mrieker/hode/freecads/backpanandacc.FCStd

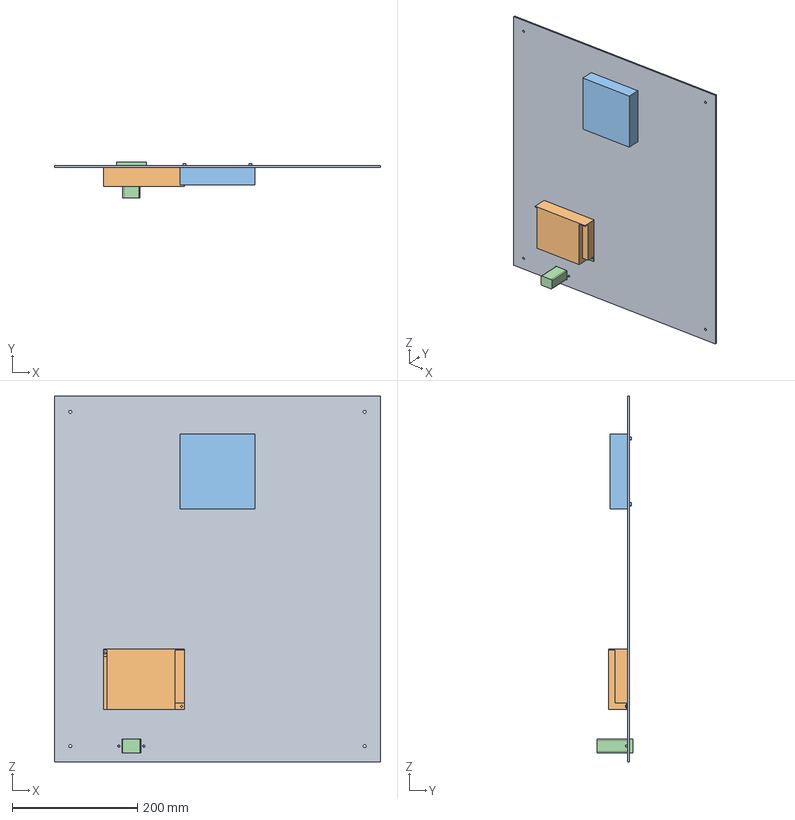
[picture p17: CAD file, 2022-03-06]
freecads/backpanandacc.FCStd
520.7 x 57.7 x 584.2 mm
backpanel_001
powersup_001
120mmfan_001
acpwrcon_001
