mrieker/hode/freecads/raspibrkt.FCStd

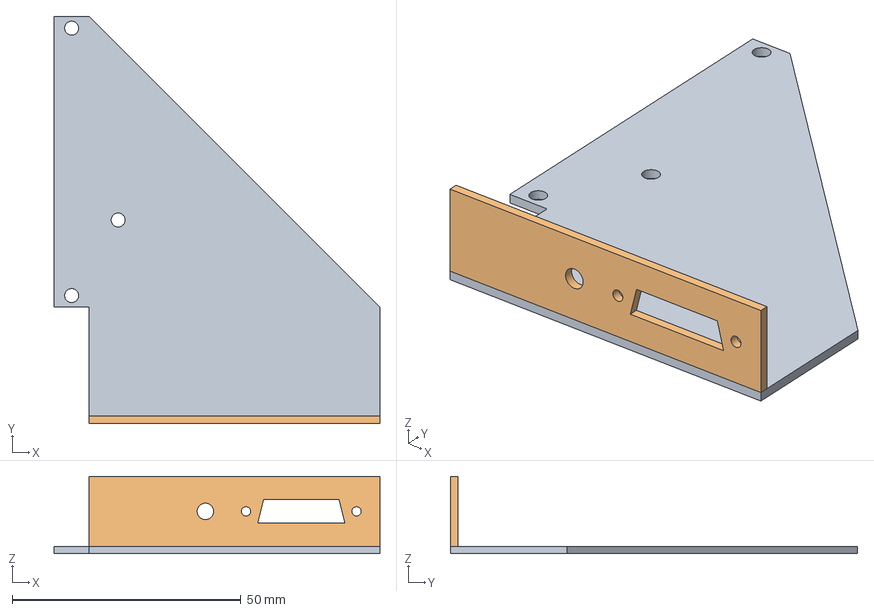
[picture p18: CAD file, 2022-03-06]
freecads/raspibrkt.FCStd
71.1 x 88.9 x 16.8 mm
raspi_base
raspi_cons
