mrieker/hode/freecads/backpanel.FCStd

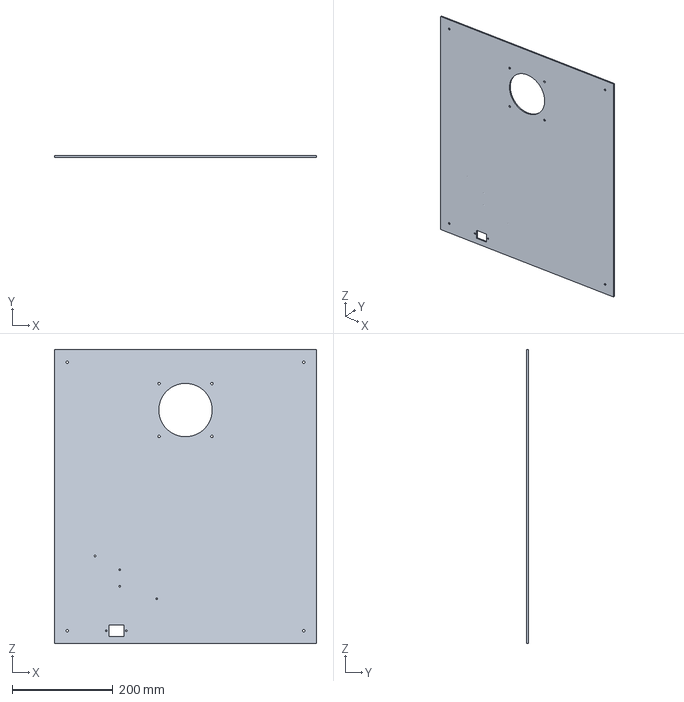
[picture p19: CAD file, 2022-03-06]
freecads/backpanel.FCStd
520.7 x 3.18 x 584.2 mm
