mrieker/hode/driver/raseqhaltloop.cc

//    Copyright (C) Mike Rieker, Beverly, MA USA
//    www.outerworldapps.com
//
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
//    EXPECT it to FAIL when someone's HeALTh or PROpeRTy is at RISk.
//
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
//    http://www.gnu.org/licenses/gpl-2.0.html

// do loop of halt instruction on RAS,SEQ board combination
// sequences through FETCH1,FETCH2,HALT1 states for electric testing
// optionally have LED board and C paddle
//  sudo insmod km/enabtsc.ko
//  . ./iow56sns.si
//  sudo -E ./raseqhaltloop.armv7l [-bpt] [-cpuhz 200]

// typically run at -cpuhz 500000
// does a SIGTRAP for gdb breakpoint at 100 errors

#include <signal.h>
#include <stdio.h>
#include <stdlib.h>
#include <string.h>
#include <time.h>

#include "gpiolib.h"
#include "miscdefs.h"

#define ST_RESET0  "RESET0",  0, G_READ | G_WRITE | G_HALT, 0, C_ALU_BONLY | C_MEM_WORD | C_PSW_IE
#define ST_RESET1  "RESET1",  0, G_READ | G_WRITE | G_HALT, C_BMUX_CON_0 | C_ALU_BONLY | C_GPRS_WE7 | C_PSW_WE | C__PSW_IECLR, C_MEM_WORD

#define ST_FETCH1  "FETCH1",  G_WORD | G_READ, G_WRITE | G_HALT, C_GPRS_REA7 | C_BMUX_CON_0 | C_ALU_ADD | C_MEM_READ | C_MEM_WORD, C_PSW_IE
#define ST_FETCH2  "FETCH2",  0, G_READ | G_WRITE | G_HALT, C_GPRS_REA7 | C_BMUX_CON_2 | C_ALU_ADD | C_GPRS_WE7 | C__IR_WE, C_MEM_WORD | C_PSW_IE

#define ST_BCC1    "BCC1",    0, G_READ | G_WRITE | G_HALT, C_GPRS_REA7 | C_BMUX_IRBROF | C_ALU_ADD, C_MEM_WORD | C_GPRS_WE7 | C_PSW_IE

#define ST_ARITH1  "ARITH1",  0, G_READ | G_WRITE | G_HALT, C_GPRS_REA | C_GPRS_REB | C_ALU_IRFC | C_GPRS_WED | C_PSW_ALUWE, C_MEM_WORD | C_PSW_IE

#define ST_STORE1  "STORE1",  G_WRITE, G_READ | G_HALT, C_GPRS_REA | C_BMUX_IRLSOF | C_ALU_ADD | C_MEM_WRITE, C_PSW_IE | C_MEM_WORD
#define ST_STORE2  "STORE2",  0, G_READ | G_WRITE | G_HALT, C_GPRS_RED2B | C_ALU_BONLY, C_MEM_WORD | C_PSW_IE

#define ST_LDA1    "LDA1",    0, G_READ | G_WRITE | G_HALT, C_GPRS_REA | C_BMUX_IRLSOF | C_ALU_ADD | C_GPRS_WED, C_MEM_WORD | C_PSW_IE

#define ST_LOAD1   "LOAD1",   G_READ, G_WRITE | G_HALT, C_GPRS_REA | C_BMUX_IRLSOF | C_ALU_ADD | C_MEM_READ, C_PSW_IE | C_MEM_WORD
#define ST_LOAD2   "LOAD2",   0, G_READ | G_WRITE | G_HALT, C_MEM_REB | C_ALU_BONLY | C_GPRS_WED, C_PSW_IE | C_MEM_WORD
#define ST_LOAD3   "LOAD3",   0, G_READ | G_WRITE | G_HALT, C_GPRS_REA7 | C_BMUX_CON_2 | C_ALU_ADD | C_GPRS_WE7, C_MEM_WORD | C_PSW_IE

#define ST_IREQ1   "IREQ1",   G_WORD | G_WRITE, G_READ | G_HALT, C_BMUX_CON__4 | C_BMUX_CON_2 | C_ALU_BONLY | C_MEM_WRITE | C_MEM_WORD, C_PSW_IE
#define ST_IREQ2   "IREQ2",   0, G_READ | G_WRITE | G_HALT, C__PSW_REB | C_ALU_BONLY, C_MEM_WORD | C_PSW_IE
#define ST_IREQ3   "IREQ3",   G_WORD | G_WRITE, G_READ | G_HALT, C_BMUX_CON__4 | C_ALU_BONLY | C_MEM_WRITE | C_MEM_WORD, C_PSW_IE
#define ST_IREQ4   "IREQ4",   0, G_READ | G_WRITE | G_HALT, C__PSW_IECLR | C_GPRS_REA7 | C_BMUX_CON_0 | C_ALU_ADD, C_MEM_WORD
#define ST_IREQ5   "IREQ5",   0, G_READ | G_WRITE | G_HALT, C_BMUX_CON_2 | C_ALU_BONLY | C_GPRS_WE7, C_MEM_WORD

#define ST_HALT1   "HALT1",   G_HALT, G_READ | G_WRITE, C_HALT | C_GPRS_REB | C_ALU_BONLY, C_MEM_WORD | C_PSW_IE

#define ST_IRET1   "IRET1",   G_WORD | G_READ, G_WRITE | G_HALT, C_BMUX_CON__4 | C_ALU_BONLY | C_MEM_READ | C_MEM_WORD, C_PSW_IE
#define ST_IRET2   "IRET2",   0, G_READ | G_WRITE | G_HALT, C_MEM_REB | C_MEM_WORD | C_ALU_BONLY | C_GPRS_WE7, C_PSW_IE
#define ST_IRET3   "IRET3",   G_WORD | G_READ, G_WRITE | G_HALT, C_BMUX_CON__4 | C_BMUX_CON_2 | C_ALU_BONLY | C_MEM_READ | C_MEM_WORD, C_PSW_IE
#define ST_IRET4   "IRET4",   0, G_READ | G_WRITE | G_HALT, C_MEM_REB | C_MEM_WORD | C_ALU_BONLY | C_PSW_WE, C_PSW_IE

#define ST_WRPS1   "WRPS1",   0, G_READ | G_WRITE | G_HALT, C_GPRS_REB | C_ALU_BONLY | C_PSW_WE, C_MEM_WORD | C_PSW_IE

#define ST_RDPS1   "RDPS1",   0, G_READ | G_WRITE | G_HALT, C__PSW_REB | C_ALU_BONLY | C_GPRS_WED, C_MEM_WORD | C_PSW_IE

static GpioLib *gpio;
static uint64_t ncycles;

static void verifystate (char const *name, uint32_t gset, uint32_t gclr, uint32_t cset, uint32_t cign);

int main (int argc, char **argv)
{
    bool bptonerror = false;
    uint32_t cpuhz = DEFCPUHZ;

    setlinebuf (stdout);

    for (int i = 0; ++ i < argc;) {
        if (strcasecmp (argv[i], "-bpt") == 0) {
            bptonerror = true;
            continue;
        }
        if (strcasecmp (argv[i], "-cpuhz") == 0) {
            if ((++ i >= argc) || (argv[i][0] == '-')) {
                fprintf (stderr, "-cpuhz missing freq\n");
                return 1;
            }
            cpuhz = atoi (argv[i]);
            continue;
        }
        if (argv[i][0] == '-') {
            fprintf (stderr, "unknown option %s\n", argv[i]);
            return 1;
        }
        fprintf (stderr, "unknown argument %s\n", argv[i]);
        return 1;
    }

    gpio = new PhysLib (cpuhz);
    gpio->open ();

    gpio->writegpio (false, G_RESET);
    gpio->halfcycle ();
    gpio->halfcycle ();
    gpio->halfcycle ();
    gpio->writegpio (false, 0);
    verifystate (ST_RESET0);
    gpio->writegpio (false, 0);
    gpio->halfcycle ();
    ncycles ++;
    gpio->writegpio (false, G_CLK);
    gpio->halfcycle ();
    verifystate (ST_RESET1);

    uint32_t lasttime = time (NULL);
    uint64_t lastcycs = 0;

    uint32_t errors   = 0;
    uint32_t lastsamp = 0;

    uint16_t opcode   = 0x0070; // HALT %R7
    uint16_t nextpc   = 0;

    while (true) {
        uint32_t thistime = time (NULL);
        if (thistime / 60 > lasttime / 60) {
            printf ("%02u:%02u:%02u %4u %13llu cycles  %6llu Hz  %10.3f uS\n",
                        thistime / 3600 % 24, thistime / 60 % 60, thistime % 60,
                        errors, ncycles, (ncycles - lastcycs) / (thistime - lasttime),
                        (thistime - lasttime) * 1000000.0 / (ncycles - lastcycs));
            lasttime = thistime;
            lastcycs = ncycles;
        }

        // halfway through the cycle with clock still high, so drop clock
        // if previous cycle was FETCH1, we are probably halfway through FETCH2, so start sending opcode to be latched in IR

        if ((lastsamp & G_INS) == (G_WORD|G_READ)) {
            gpio->writegpio (true, opcode * G_DATA0);
        } else {
            gpio->writegpio (false, 0);
        }

        // wait for end of cycle then sample GPIO pins
        gpio->halfcycle ();
        uint32_t sample = gpio->readgpio ();

        // decode the input pins to see what cycle we are at
        switch (sample & G_INS) {

            // currently at end of FETCH1
            case G_WORD|G_READ: {
                if ((lastsamp & G_INS) != (G_WORD|G_HALT)) {
                    printf ("%4u %13llu FETCH1 not preceded by HALT: %08X %s\n", ++ errors, ncycles, lastsamp, GpioLib::decocon (CON_G, lastsamp).c_str ());
                }
                uint16_t pc = sample / G_DATA0;
                if (pc != nextpc) {
                    printf ("%4u %13llu FETCH1 PC is %04X expected %04X\n", ++ errors, ncycles, pc, nextpc);
                }
                nextpc = pc + 2;
                break;
            }

            // currently at end of FETCH2
            case G_WORD: {
                if ((lastsamp & G_INS) != (G_WORD|G_READ)) {
                    printf ("%4u %13llu FETCH2 not preceded by FETCH1: %08X %s\n", ++ errors, ncycles, lastsamp, GpioLib::decocon (CON_G, lastsamp).c_str ());
                }
                break;
            }

            // currently at end of HALT
            case G_WORD|G_HALT: {
                if ((lastsamp & G_INS) != (G_WORD)) {
                    printf ("%4u %13llu HALT not preceded by FETCH2: %08X %s\n", ++ errors, ncycles, lastsamp, GpioLib::decocon (CON_G, lastsamp).c_str ());
                }
                uint16_t pc = sample / G_DATA0;
                if (pc != nextpc) {
                    printf ("%4u %13llu HALT PC is %04X expected %04X\n", ++ errors, ncycles, pc, nextpc);
                }
                break;
            }

            default: {
                printf ("%4u %13llu unknown cycle: %08X %s\n", ++ errors, ncycles, lastsamp, GpioLib::decocon (CON_G, lastsamp).c_str ());
                break;
            }
        }
        if (errors > 99) {
            if (! bptonerror) break;
            raise (SIGTRAP);
        }
        lastsamp = sample;

        // at end of cycle with clock still low, drive clock high
        // if we are ending FETCH2, keep outputting the opcode so it gets latched in IR properly

        ncycles ++;
        if ((lastsamp & G_INS) == (G_WORD)) {
            gpio->writegpio (true, (opcode * G_DATA0) | G_CLK);
        } else {
            gpio->writegpio (false, G_CLK);
        }

        // wait until halfway through the new cycle
        gpio->halfcycle ();
    }

    return 0;
}

static void verifystate (char const *name, uint32_t gset, uint32_t gclr, uint32_t cset, uint32_t cign)
{
    uint32_t gactual = gpio->readgpio ();
    if ((gactual & (gset | gclr)) != gset) {
        fprintf (stderr, "verifystate: should be in state %s\n", name);
        if ((gset | gclr) & G_READ)  fprintf (stderr, "G_READ  is %s expect %s\n", (gactual & G_READ)  ? "set" : "clr", (gset & G_READ)  ? "set" : "clr");
        if ((gset | gclr) & G_WRITE) fprintf (stderr, "G_WRITE is %s expect %s\n", (gactual & G_WRITE) ? "set" : "clr", (gset & G_WRITE) ? "set" : "clr");
        if ((gset | gclr) & G_WORD)  fprintf (stderr, "G_WORD  is %s expect %s\n", (gactual & G_WORD)  ? "set" : "clr", (gset & G_WORD)  ? "set" : "clr");
        if ((gset | gclr) & G_HALT)  fprintf (stderr, "G_HALT  is %s expect %s\n", (gactual & G_HALT)  ? "set" : "clr", (gset & G_HALT)  ? "set" : "clr");
        abort ();
    }

/*
    uint32_t cactual;
    if (gpio->readcon (CON_C, &cactual)) {
        cactual ^= C_FLIP;
        cactual &= C_SEQ;
        if (((cactual & cset) != cset) || ((cactual & ~ cign & ~ cset) != 0)) {
            fprintf (stderr, "verifystate: should be in state %s\n", name);
            fprintf (stderr, "ccon expect set %s\n", GpioLib::decocon (CON_C, (  cset    & ~ cign) ^ C_FLIP).c_str ());
            fprintf (stderr, "     actual set %s\n", GpioLib::decocon (CON_C, (  cactual & ~ cign) ^ C_FLIP).c_str ());
            fprintf (stderr, "ccon expect clr %s\n", GpioLib::decocon (CON_C, (~ cset    & ~ cign) ^ C_FLIP).c_str ());
            fprintf (stderr, "     actual clr %s\n", GpioLib::decocon (CON_C, (~ cactual & ~ cign) ^ C_FLIP).c_str ());
            abort ();
        }
    }
*/
}
